kauzerei/openautolab/parts/enclosure.scad

// Box that encloses OpenAutoLab electronics.
//
// Copyright (c) 2023-2024 Kauzerei <mailto:openautolab@kauzerei.de>
//
// This program is free software: you can redistribute it and/or modify
// it under the terms of the GNU General Public License as published by
// the Free Software Foundation, either version 3 of the License, or
// (at your option) any later version.
//
// This program is distributed in the hope that it will be useful,
// but WITHOUT ANY WARRANTY; without even the implied warranty of
// MERCHANTABILITY or FITNESS FOR A PARTICULAR PURPOSE. See the
// GNU General Public License for more details.
//
// You should have received a copy of the GNU General Public License
// along with this program. If not, see <https://www.gnu.org/licenses/>.

$fs=1/2;
$fa=1/1;
bissl=1/100;
part="Front"; //[Front, Back, Buttons, Battery enclosure]
tolerance=0.5;
pcb_width=109.22;
pcb_height=74.93;
pcb_offset=26;
pcb_thickness=2;
solder_thickness=2;
mount_hole=4.5;
pcb_holes_pos=[[3.81,3.81],[105.41,3.8],[3.8,71.12],[105.41,71.12]];
wall=1.6;
buttons_pos=[[22,69.6],[54.6,69.6],[86.8,69.6]];
buttons_outer=10;
buttons_inner=4;
buttons_height=5;
//array of connectors, each connector=[[posx,posy,posz],[sizex,sizey,sizez]]
small_offset_z=pcb_offset+pcb_thickness+solder_thickness+wall-5;
wide_offset_z=pcb_offset+pcb_thickness+solder_thickness+wall-9;
connectors=[ //top:
             [[10.67,0,small_offset_z],[7,18,10]],
             [[19.56,0,small_offset_z],[7,18,10]],
             [[28.45,0,small_offset_z],[7,18,10]],
             [[37.34,0,small_offset_z],[7,18,10]],
             [[46.23,0,small_offset_z],[7,18,10]],
             [[55.12,0,small_offset_z],[7,18,10]],
             [[64,0,small_offset_z],[7,18,10]],
             [[72.0,0,small_offset_z],[7,18,10]],
             [[83.82,0,small_offset_z],[7,18,10]],
             [[96.52,0,small_offset_z],[7,18,10]],
             //left:
             [[0,30.5,small_offset_z],[20,10,10]],
             [[0,48.26,wide_offset_z],[20,10,18]],
             //right:
             [[109,21.59,small_offset_z],[20,10,10]],
             [[109,40.64,wide_offset_z],[20,10,18]],
             [[109,55.88,small_offset_z],[20,10,10]]
           ];
switches_pos=[[91,0,11],[78,0,11]];
switches_diameter=7;
screen_pos=[54.5,35];
screen_mount=[93,55];
screen_mount_holes=3;
screen_rect=[98.5,41];

battery_h=90;
battery_w=85;
battery_d=22;

module front() {
  difference() {
    translate([-tolerance-wall,-tolerance-wall,bissl])cube([pcb_width+2*tolerance+2*wall,pcb_height+2*tolerance+2*wall,wall]);
    for (i=[[[1,0],[0,1]],[[-1,0],[0,1]],[[1,0],[0,-1]],[[-1,0],[0,-1]]])translate(screen_pos)translate(i*screen_mount/2)cylinder(d=screen_mount_holes,h=wall+2*bissl);
    translate(screen_pos-screen_rect/2)cube([screen_rect[0],screen_rect[1],wall+2*bissl]);
    for(tr=buttons_pos) translate(tr) cylinder(d=buttons_inner+2*tolerance,h=pcb_offset-buttons_height-2+wall+2*bissl);
  }
  difference() {
    translate([0,0,wall])cube([pcb_width,pcb_height,mount_hole/2]);
    translate([wall,wall,wall-bissl])cube([pcb_width-2*wall,pcb_height-2*wall,mount_hole/2+2*bissl]);
  }
  difference() {
    for (i=[[0,0,wall],[0,pcb_height-2*mount_hole,wall],[pcb_width-mount_hole,0,wall],[pcb_width-mount_hole,pcb_height-2*mount_hole,wall]]) translate(i) difference() {
    cube([mount_hole,2*mount_hole,2*mount_hole]);
    translate([-bissl,mount_hole,mount_hole])rotate([0,90,0])cylinder(h=2*mount_hole+2*bissl,d=mount_hole);}
  }
  difference() {
    translate([0,0,wall])for (tr = buttons_pos) translate(tr) cylinder(d=buttons_outer,h=pcb_offset-buttons_height+pcb_thickness+solder_thickness-2);
    translate([0,0,wall-bissl])for(tr=buttons_pos) translate(tr) cylinder(d=buttons_inner+2*tolerance,h=pcb_offset-buttons_height+pcb_thickness+solder_thickness+2*bissl);
  }
  difference() {
    translate([0,0,wall]) for (i=[[[1,0],[0,1]],[[-1,0],[0,1]],[[1,0],[0,-1]],[[-1,0],[0,-1]]])translate(screen_pos)translate(i*screen_mount/2) cylinder(d=screen_mount_holes*2,h=solder_thickness);
    translate([0,0,wall-bissl])for (i=[[[1,0],[0,1]],[[-1,0],[0,1]],[[1,0],[0,-1]],[[-1,0],[0,-1]]])translate(screen_pos)translate(i*screen_mount/2) cylinder(d=screen_mount_holes,h=solder_thickness+2*bissl);
  }
}

module back() {
  difference() {
    translate([-tolerance-wall,-tolerance-wall,0])
    cube([pcb_width+2*wall+2*tolerance,pcb_height+2*wall+2*tolerance,pcb_offset+2*pcb_thickness+2*solder_thickness+2*wall]);
    difference() {
      translate([-tolerance,-tolerance,-bissl])cube([pcb_width+2*tolerance,pcb_height+2*tolerance,pcb_offset+2*pcb_thickness+2*solder_thickness+wall+bissl]);
      translate([0,0,pcb_offset+2*pcb_thickness+solder_thickness+wall+bissl])for (i=pcb_holes_pos)translate(i)cylinder(d=mount_hole*2,h=solder_thickness);
    }
  translate([0,0,pcb_offset+2*pcb_thickness+solder_thickness+wall-bissl])for (i=pcb_holes_pos)translate(i)cylinder(d=mount_hole,h=wall+solder_thickness+2*bissl);
  for (i=connectors) {
    pose=i[0];
    size=i[1];
    translate(pose) cube(size,center=true);
  }
  for (pose=switches_pos) translate(pose) rotate([90,0,0])cylinder(d=8,h=10,center=true); //switches
  for (i=[[-wall-tolerance-bissl,0,0],[-wall-tolerance-bissl,pcb_height-2*mount_hole,0],[pcb_width+tolerance-bissl,0,0],[pcb_width+tolerance-bissl,pcb_height-2*mount_hole,0]]) translate(i) translate([-bissl,mount_hole,mount_hole])rotate([0,90,0])cylinder(h=wall+4*bissl,d=mount_hole);
  }
}

module buttons() {
  cylinder(d=buttons_outer,h=2);
  translate([0,0,2])cylinder(d=buttons_inner,h=pcb_offset-buttons_height+pcb_thickness+solder_thickness+wall+2);
}

module battery_enclosure() {
  part_width=2*mount_hole;
  part_thickness=wall;
  difference() {
    union() {
      cube([battery_w+2*wall,battery_d+2*wall,battery_h+wall]);
      translate([-part_width,0,0])cube([battery_w+2*wall+2*part_width,wall,battery_h+wall]);
    }
    translate([wall,wall,wall+bissl]) cube([battery_w,battery_d,battery_h]);
    for (tr=[[-part_width/2,-bissl,part_width/2],
             [2*wall+part_width/2+battery_w,-bissl,part_width/2],
             ])
      translate(tr)rotate([-90,0,0]) cylinder(d=mount_hole,h=wall+2*bissl);
  }
}

if (part=="Front") front();
if (part=="Back") rotate([180,0,0])back();
if (part=="Buttons") buttons();
if (part=="Battery enclosure") battery_enclosure();
