kauzerei/openautolab/parts/upper_rail.scad

// Upper rail parts of OpenAutoLab: mounting brackets for valves, for pumps and for electronic enclosure
//
// Copyright (c) 2023-2024 Kauzerei <mailto:openautolab@kauzerei.de>
//
// This program is free software: you can redistribute it and/or modify
// it under the terms of the GNU General Public License as published by
// the Free Software Foundation, either version 3 of the License, or
// (at your option) any later version.
//
// This program is distributed in the hope that it will be useful,
// but WITHOUT ANY WARRANTY; without even the implied warranty of
// MERCHANTABILITY or FITNESS FOR A PARTICULAR PURPOSE. See the
// GNU General Public License for more details.
//
// You should have received a copy of the GNU General Public License
// along with this program. If not, see <https://www.gnu.org/licenses/>.

$fs=1/2;
$fa=1/1;
bissl=1/100;
part = "Valve_bracket"; // [Valve_bracket, Main_pump_bracket, Filter_pump_type1_bracket, Filter_pump_type2_bracket, Filter_attachment]
/* [Rail general parameters] */
rod_diameter=8;
rods_distance=62;

/* [mounts parameters] */
mount_hole=4.5;
part_thickness=3;
part_width=2*mount_hole+part_thickness;
tightening_gap=1;
pump_offset=5;
mount_hole_distance=38;

/* [Filter attachment options] */
filter_wall=6;
offset_v=20;
offset_h=12;
hole=9;

module hole(mount_hole=4.5) { //hole for clamping with threaded screw
  cylinder(d=mount_hole,h=100,center=true);
  mirror([0,0,1])cylinder(d=mount_hole*2,h=100,$fn=6);
}

module pumpholes() {
  translate([rods_distance/2,0,0])circle(d=rod_diameter);
  translate([-rods_distance/2,0,0])circle(d=rod_diameter);
  translate([0,10])rotate([0,0,-50]) {
    translate([31,0])circle(d=4);
    translate([-21,0])circle(d=4);
    translate([0,0])circle(d=34);
  }
}

module main_pump_bracket() {
  pumpmounts=[[21,0],[-31,0]];
  rodmounts=[[rods_distance/2,0],[-rods_distance/2,0]];
  shift=[-5,6];
  rotation=-140;
  pumpdiameter=34;
  difference() {
    union() {
      hull() {
        translate(shift)rotate([0,0,rotation])for (i=pumpmounts) translate(i)cylinder(h=part_width,d=mount_hole+2*part_thickness,center=true);
        for (i=rodmounts) translate(i)cylinder(h=part_width,d=rod_diameter+2*part_thickness,center=true);
        translate(shift)rotate([0,0,rotation])cylinder(h=part_width,d=pumpdiameter+2*part_thickness,center=true);
      }
      translate(shift)rotate([0,0,rotation])for (i=pumpmounts) translate(i)translate([0,0,pump_offset/2])cylinder(h=part_width+pump_offset,d=mount_hole+2*part_thickness,center=true);
    }
    translate(shift)rotate([0,0,rotation])for (i=pumpmounts) translate(i)cylinder(h=part_width+2*pump_offset+bissl,d=mount_hole,center=true);
    for (i=rodmounts) translate(i)cylinder(h=part_width+bissl,d=rod_diameter,center=true);
    translate(shift)rotate([0,0,rotation])cylinder(h=part_width+2*pump_offset+bissl,d=pumpdiameter,center=true);
    cube([2*rods_distance,tightening_gap,part_width+2],center=true);
    rotate([90,0,18])translate([19,0,-part_thickness]) hole(mount_hole=mount_hole);
  }
}

module pump_shape(type) {
  if (type==1) hull(){
    circle(d=34);
    translate([17,-9])circle(d=8);
    translate([17,9])circle(d=8);
    translate([-17,-9])circle(d=8);
    translate([-17,9])circle(d=8);
  }
  if (type==2) hull(){
    translate([14,-14])circle(d=8);
    translate([-14,-14])circle(d=8);
    translate([14,14])circle(d=8);
    translate([-14,14])circle(d=8);
  }
}

module filterpump(type) {
  difference() {
    linear_extrude(height=part_width,convexity=4)difference() {
      offset (r=part_thickness) hull() {
        pump_shape(type);
        translate([rods_distance/2,9])circle(d=rod_diameter);
        translate([-rods_distance/2,9])circle(d=rod_diameter);
      }
    pump_shape(type);
    translate([rods_distance/2,9])circle(d=rod_diameter);
    translate([-rods_distance/2,9])circle(d=rod_diameter);
    translate([0,9])square([2*rods_distance,1],center=true);
    }
  translate([26,0,part_width/2])rotate([-90,0,10])hole(mount_hole=mount_hole);
  translate([-26,0,part_width/2])rotate([-90,0,-10])hole(mount_hole=mount_hole);
  }
}

module filter_attachment() {
  cube([part_thickness,2*hole,offset_v+part_thickness]);
  tail=min(20,offset_v+part_thickness);
  translate([-part_thickness-filter_wall,0,offset_v+part_thickness-tail])cube([part_thickness,2*hole,tail]);
  translate([-filter_wall,0,offset_v])cube([filter_wall,2*hole,part_thickness]);
  difference() {
    cube([offset_h+hole ,2*hole,part_thickness]);
    translate([offset_h,hole,part_thickness/2])cylinder(h=part_thickness+bissl,d=hole,center=true);
  }
}

module valve_bracket() {
  sq=rod_diameter+2*part_thickness;
  difference() {
    union() {
    for (tr=[[rods_distance/2,0,0],[-rods_distance/2,0,0]]) translate(tr)
      cylinder(d=sq, h=sq, center=true);
    hull() for (tr=[[0,sq/4,sq/4],[0,-sq/4,-sq/4]])
      translate(tr) cube([rods_distance,sq/2,sq/2],center=true);
    }
    for (tr=[[rods_distance/2,0,0],[-rods_distance/2,0,0]]) translate(tr)
      cylinder(d=rod_diameter, h=sq+1/100, center=true);
    rotate([-20,0,0]) translate([0,sq/2+tightening_gap/4,0]) cube([rods_distance+rod_diameter+2*part_thickness+1/100,sq+tightening_gap/2,2*sq],center=true);
    for (tr=[[-mount_hole_distance/2,0,2],[mount_hole_distance/2,0,2]]) rotate([45,0,0]) translate(tr) {
      cylinder(d=mount_hole,h=2*sq,center=true);
      cylinder(d=mount_hole*2,h=sq,$fn=6);
    }
  }
}

if (part=="Valve_bracket") valve_bracket();
if (part=="Main_pump_bracket") main_pump_bracket();
if (part=="Filter_pump_type1_bracket") filterpump(1);
if (part=="Filter_pump_type2_bracket") filterpump(2);
if (part=="Filter_attachment") filter_attachment();
